maibadge/maibadge/code/circuitpython-full-slop-port/assets/menu/maisongchosen.jpg

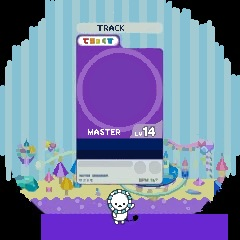
code/circuitpython-full-slop-port/assets/menu/maisongchosen.jpg
