maibadge/maibadge/graphics/images.jpg

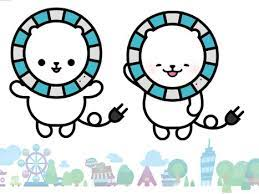
graphics/images.jpg
