maibadge/maibadge/code/circuitpython-full-slop-port/assets/gifs/ezgif-7-562f90826a.gif

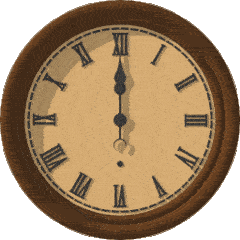
code/circuitpython-full-slop-port/assets/gifs/ezgif-7-562f90826a.gif
