maibadge/maibadge/code/circuitpython-full-slop-port/assets/gifs/maislides.gif

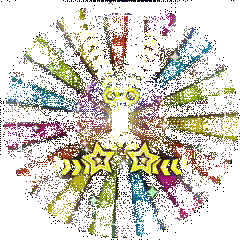
code/circuitpython-full-slop-port/assets/gifs/maislides.gif
