maibadge/maibadge/code/circuitpython/image/test_image.jpg

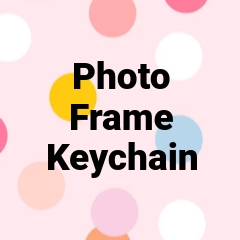
code/circuitpython/image/test_image.jpg
